OpenSourceSDRLab/PortaRF/hardware/portapack_h4m/h4-pcb/README.txt

This folder contains the PCB files for PortaPack H4. If you have any questions about the PCB files, please feel free to contact me. Thank you!

My email addresses are:
support@opensourcesdrlab.com
opensourcesdrlab@gmail.com
