OpenSourceSDRLab/PortaRF/docs/images/h2_cover.jpg

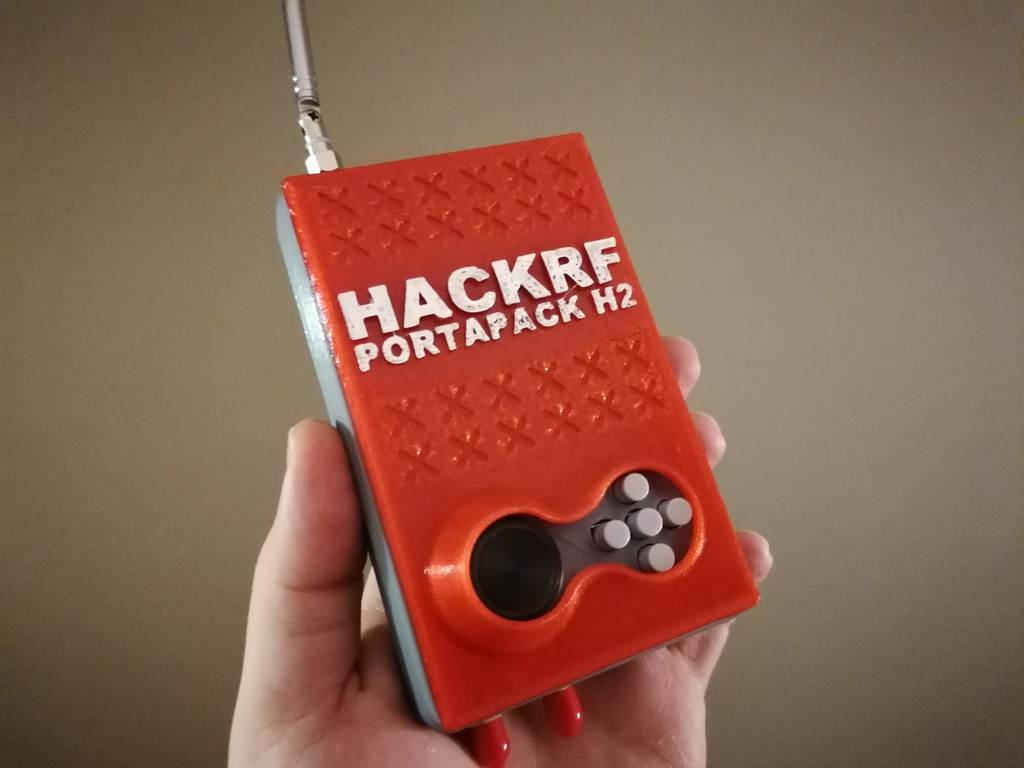
docs/images/h2_cover.jpg
