OpenSourceSDRLab/PortaRF/docs/images/h2_front.jpg

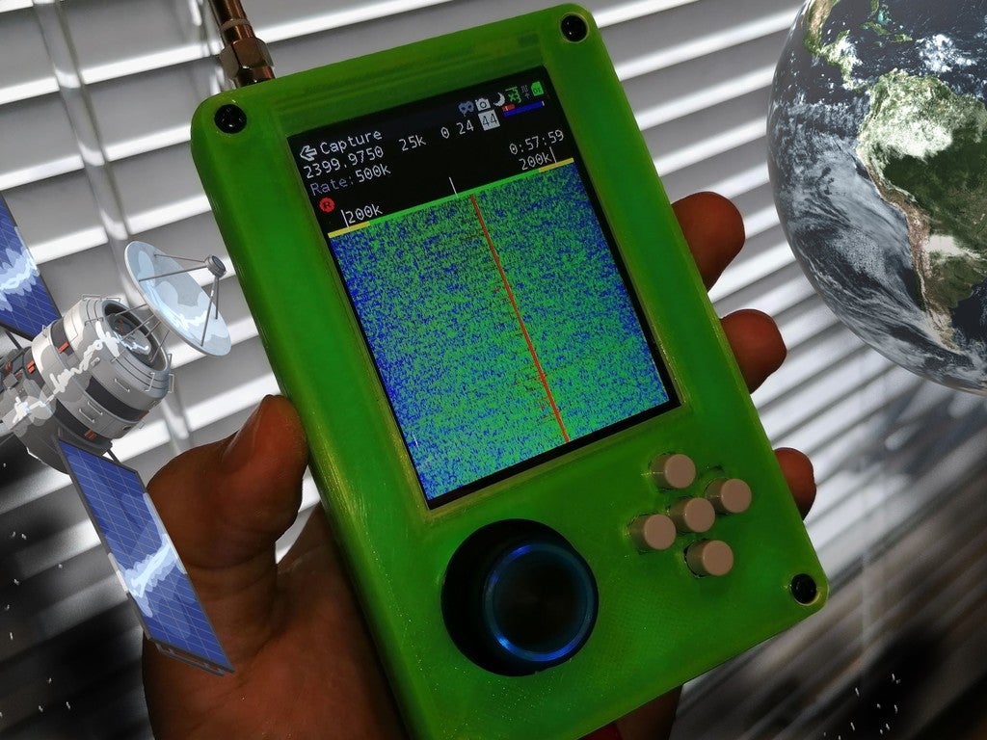
docs/images/h2_front.jpg
