OpenSourceSDRLab/PortaRF/firmware/chibios-portapack/ext/fatfs/doc/res/f7.png

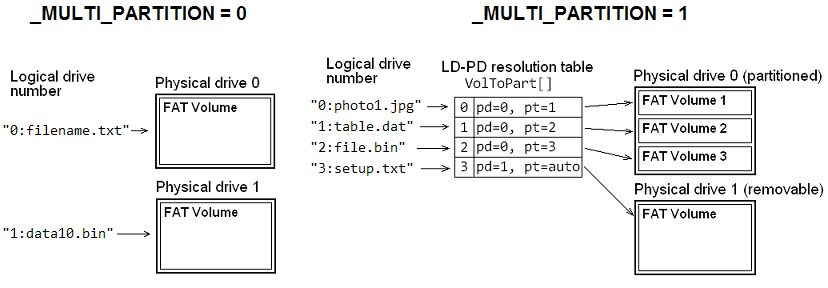
firmware/chibios-portapack/ext/fatfs/doc/res/f7.png
