OpenSourceSDRLab/PortaRF/firmware/chibios-portapack/ext/fatfs/doc/res/modules.png

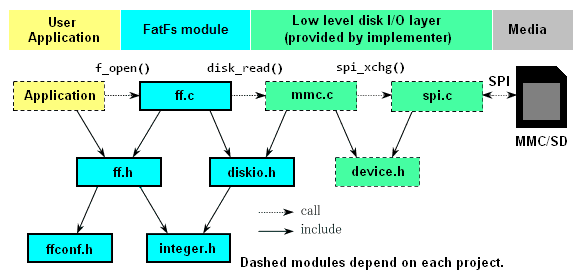
firmware/chibios-portapack/ext/fatfs/doc/res/modules.png
