OpenSourceSDRLab/PortaRF/hackrf/docs/images/block-diagram-r9.png

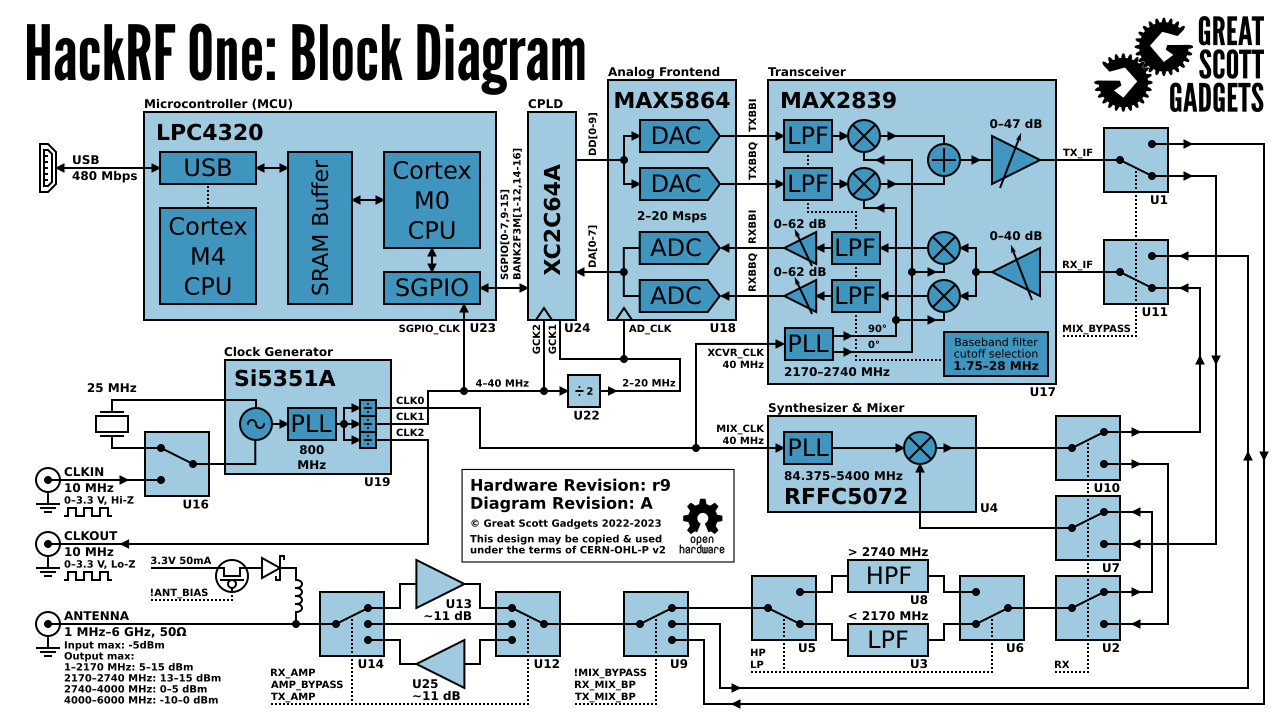
hackrf/docs/images/block-diagram-r9.png
