OpenSourceSDRLab/PortaRF/hackrf/docs/images/block-diagram.png

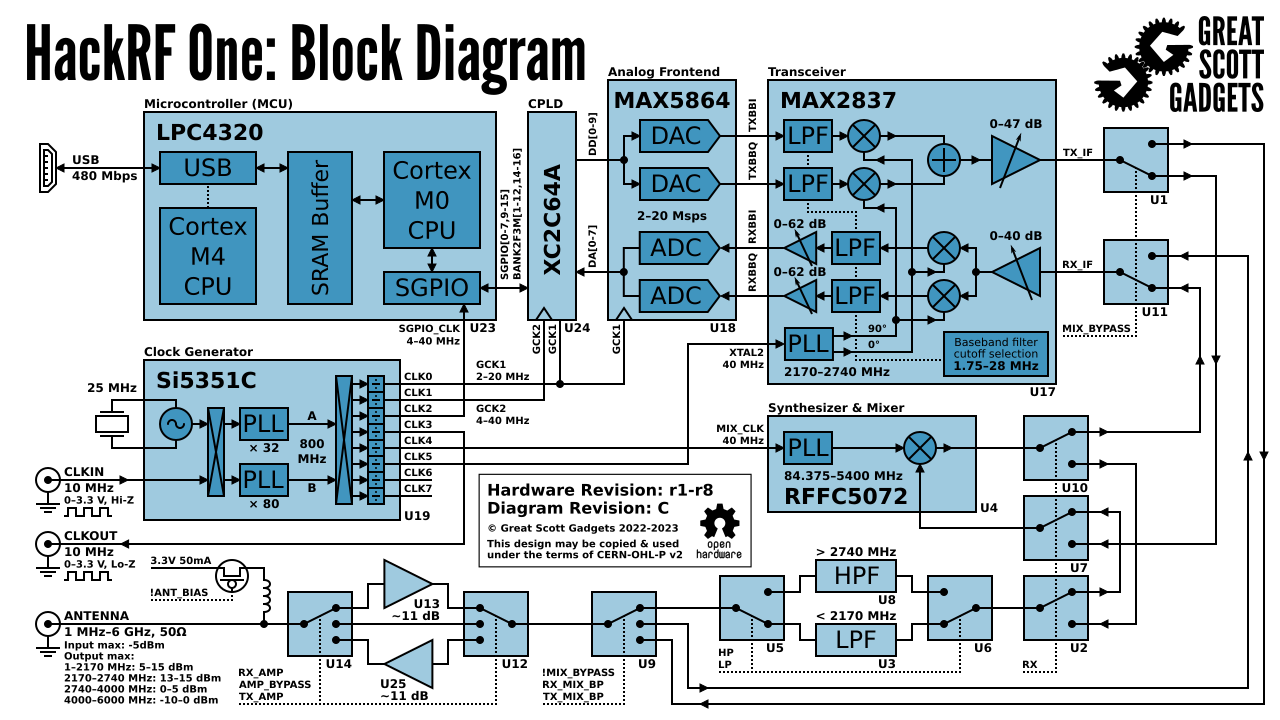
hackrf/docs/images/block-diagram.png
