OpenSourceSDRLab/PortaRF/hackrf/docs/images/grc-hw-sync-streaming.png

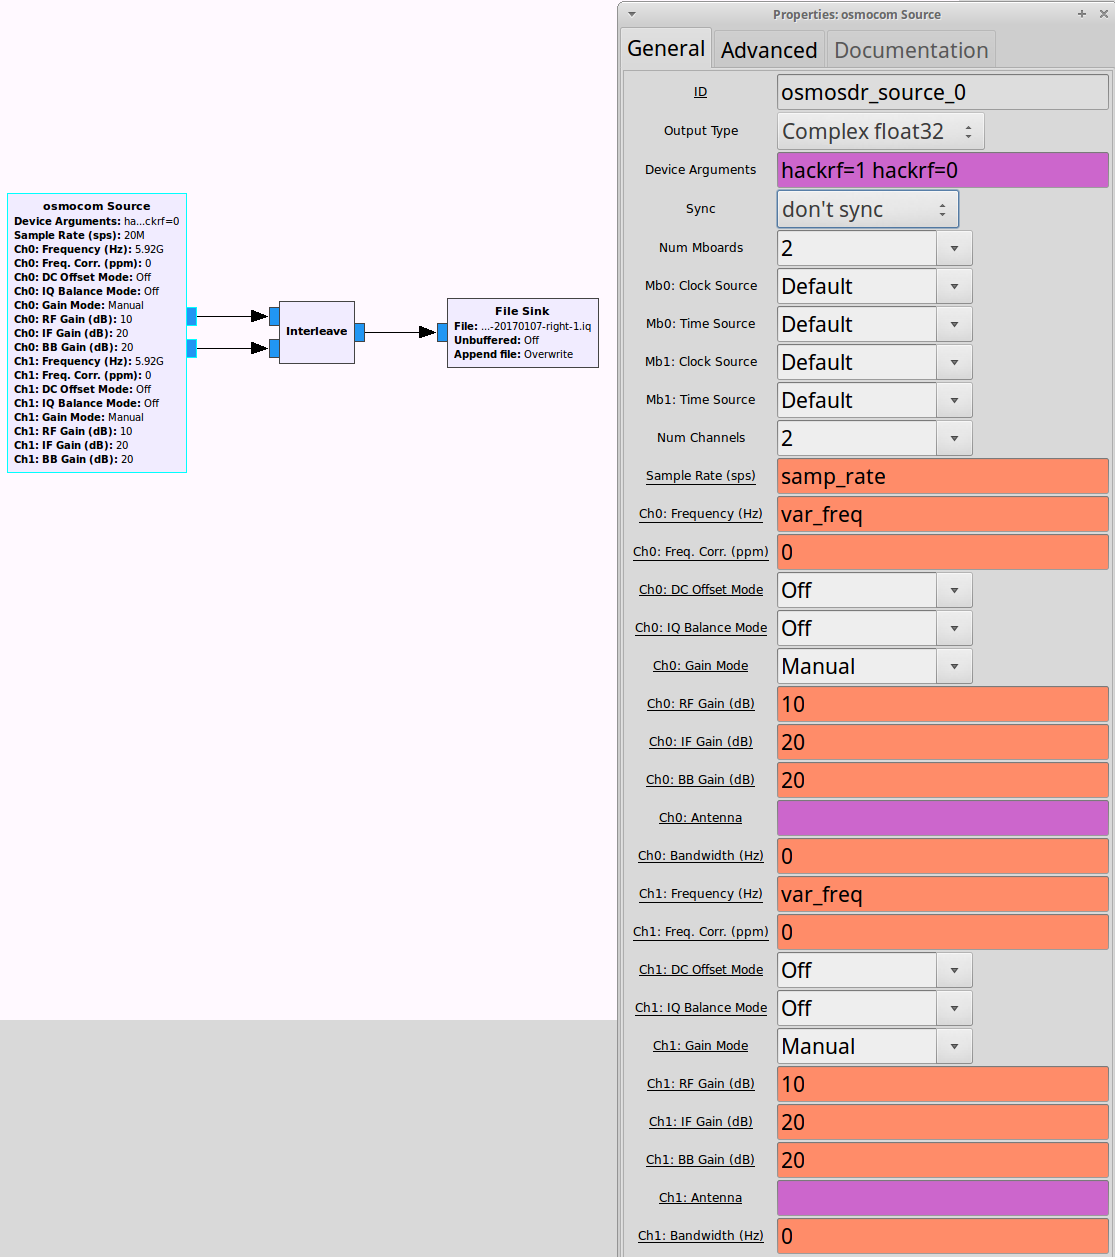
hackrf/docs/images/grc-hw-sync-streaming.png
