OpenSourceSDRLab/PortaRF/hackrf/docs/images/jawbreaker.JPG

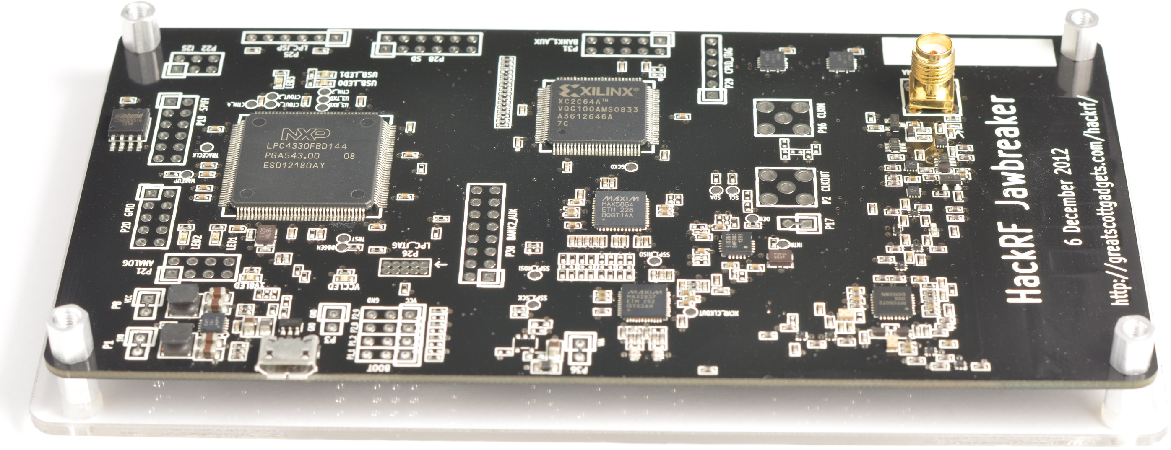
hackrf/docs/images/jawbreaker.JPG
