OpenSourceSDRLab/PortaRF/hackrf/docs/images/noisereducingcable.jpeg

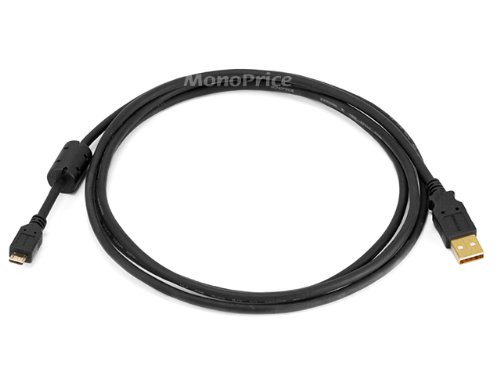
hackrf/docs/images/noisereducingcable.jpeg
