OpenSourceSDRLab/PortaRF/hackrf/docs/images/noisereducingcablescreenshot.jpeg

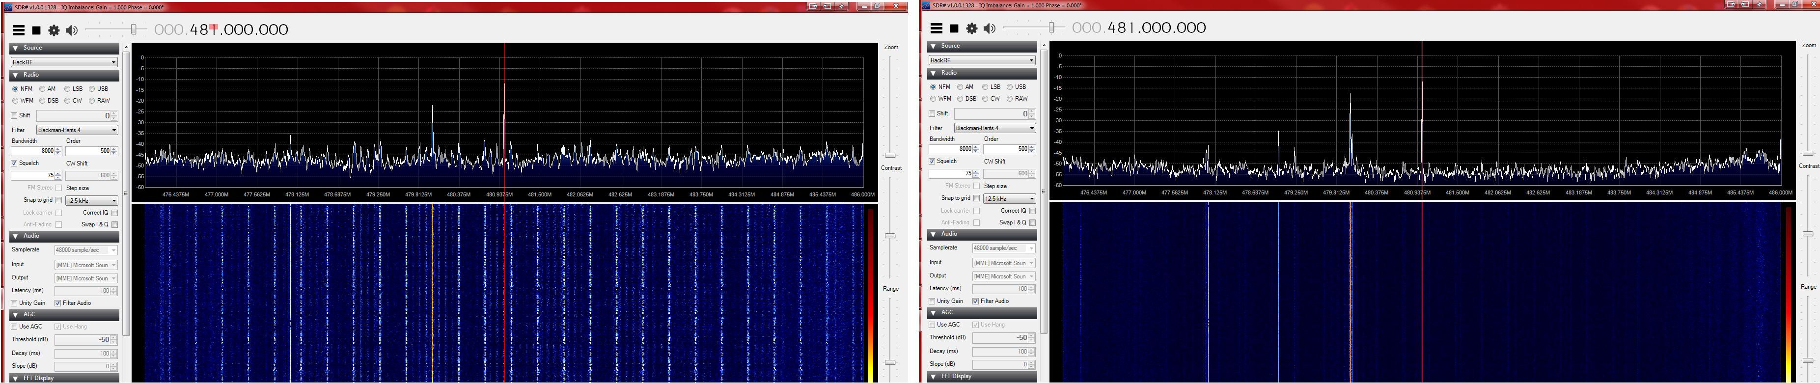
hackrf/docs/images/noisereducingcablescreenshot.jpeg
