OpenSourceSDRLab/PortaRF/hackrf/docs/images/operacake-block-diagram.png

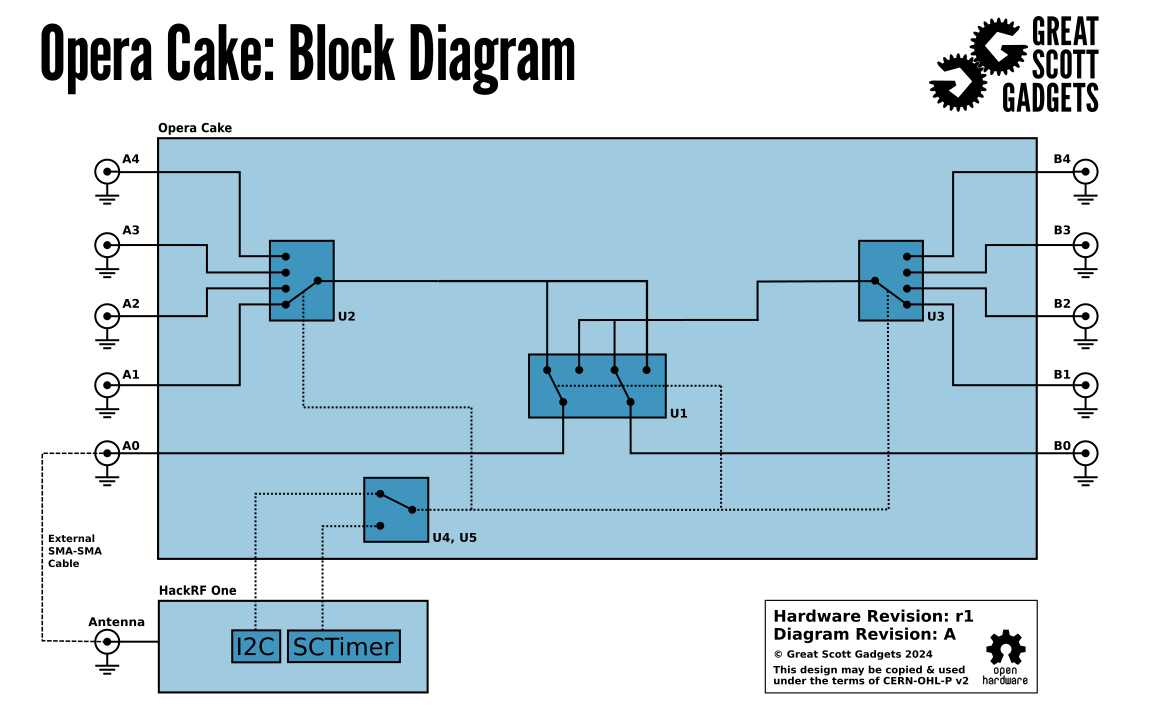
hackrf/docs/images/operacake-block-diagram.png
