OpenSourceSDRLab/PortaRF/hackrf/docs/images/operacake.jpeg

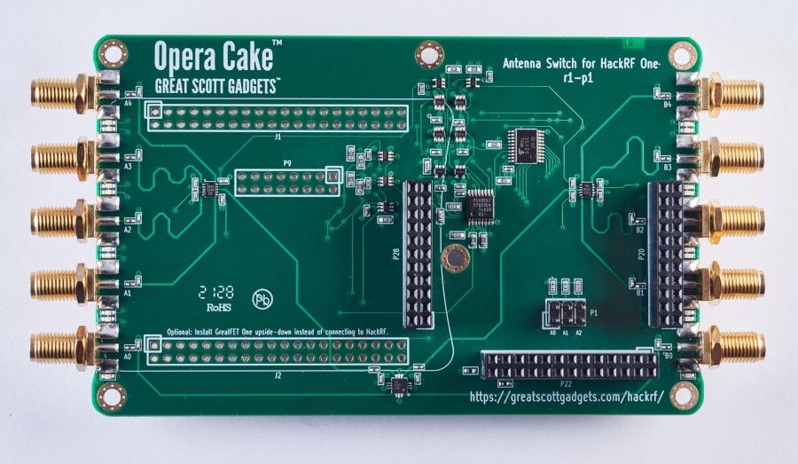
hackrf/docs/images/operacake.jpeg
