OpenSourceSDRLab/PortaRF/hackrf/docs/images/rf_shield_3.jpg

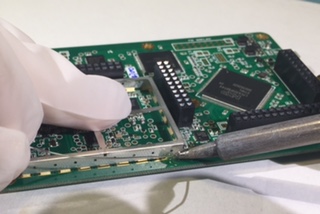
hackrf/docs/images/rf_shield_3.jpg
