OpenSourceSDRLab/PortaRF/hackrf/docs/images/rf_shield_4.jpg

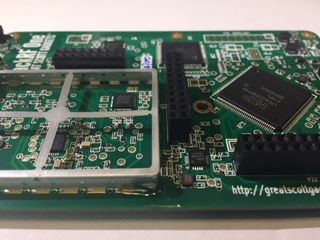
hackrf/docs/images/rf_shield_4.jpg
