OpenSourceSDRLab/PortaRF/hackrf/docs/images/rf_shield_5.jpg

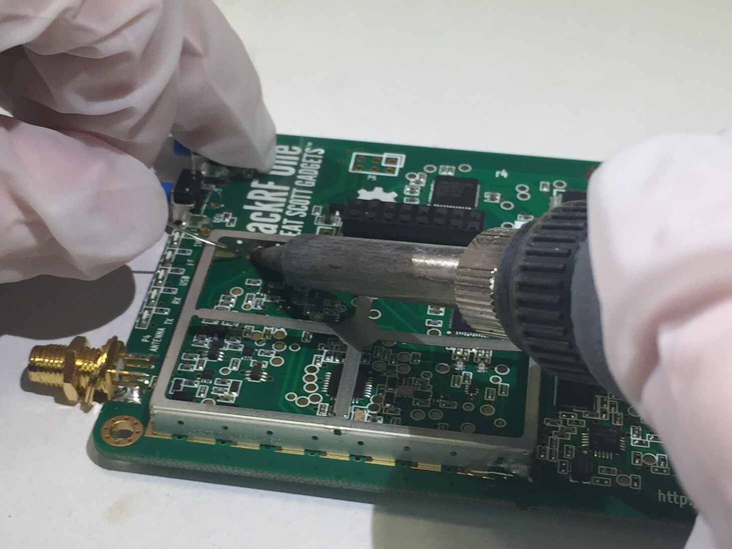
hackrf/docs/images/rf_shield_5.jpg
