OpenSourceSDRLab/PortaRF/hackrf/docs/images/rf_shield_6.jpg

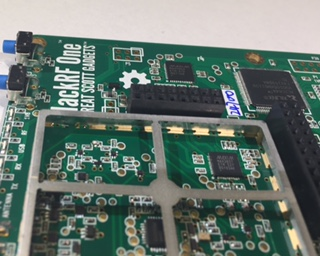
hackrf/docs/images/rf_shield_6.jpg
