OpenSourceSDRLab/PortaRF/hackrf/docs/images/trigger-pins.png

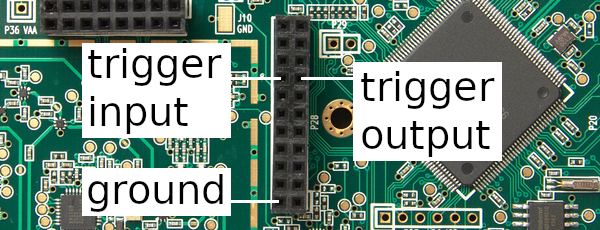
hackrf/docs/images/trigger-pins.png
