OpenSourceSDRLab/PortaRF/images/6afd1d4916e6c6b03d07bbbb10bda296.jpg

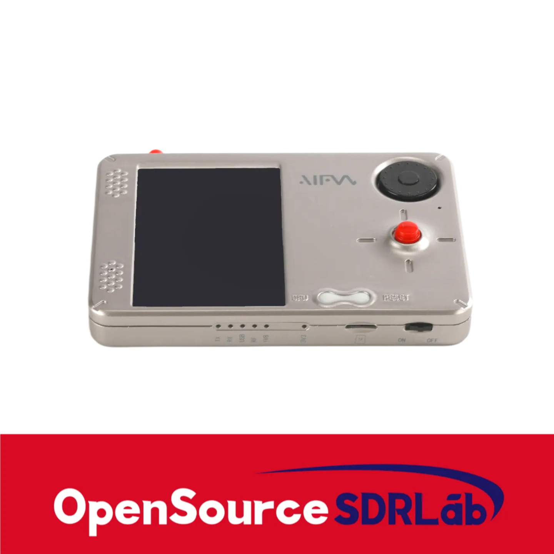
images/6afd1d4916e6c6b03d07bbbb10bda296.jpg
