OpenSourceSDRLab/PortaRF/images/069db5dcb38166e48cfb38b87b556339.jpg

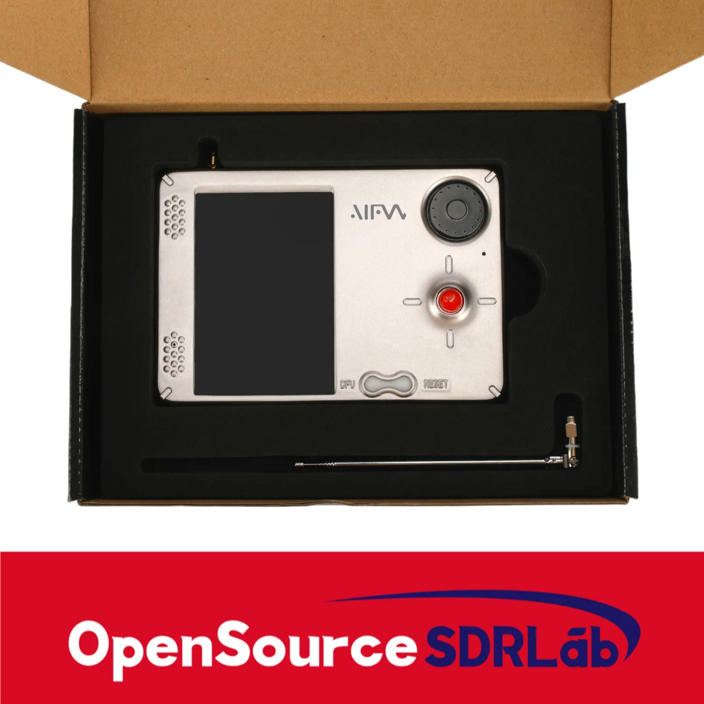
images/069db5dcb38166e48cfb38b87b556339.jpg
