OpenSourceSDRLab/PortaRF/images/0192db731e4ba467686fbc48f90995fa.jpg

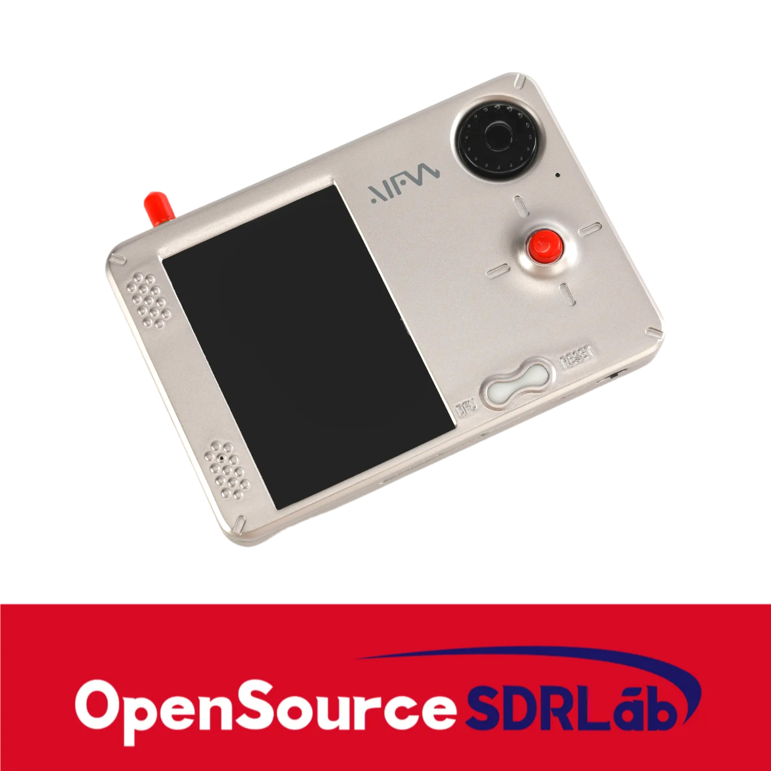
images/0192db731e4ba467686fbc48f90995fa.jpg
