OpenSourceSDRLab/PortaRF/images/1893cb14351a77d188c50b2f643207d6.jpg

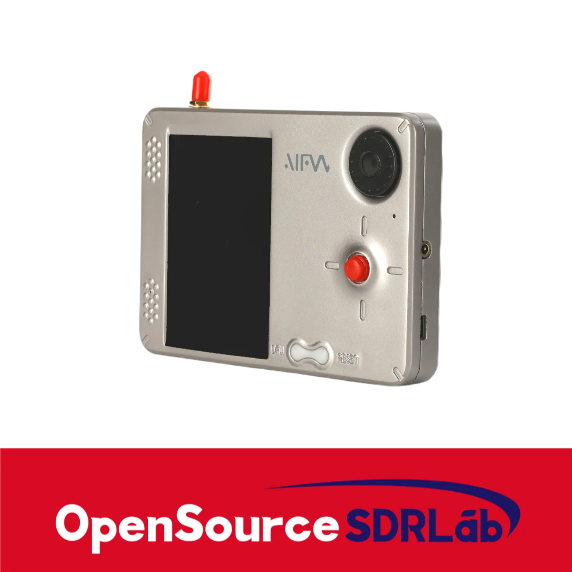
images/1893cb14351a77d188c50b2f643207d6.jpg
