OpenSourceSDRLab/PortaRF/images/09969ef1a2aa3e77349972c5e69b2ade.jpg

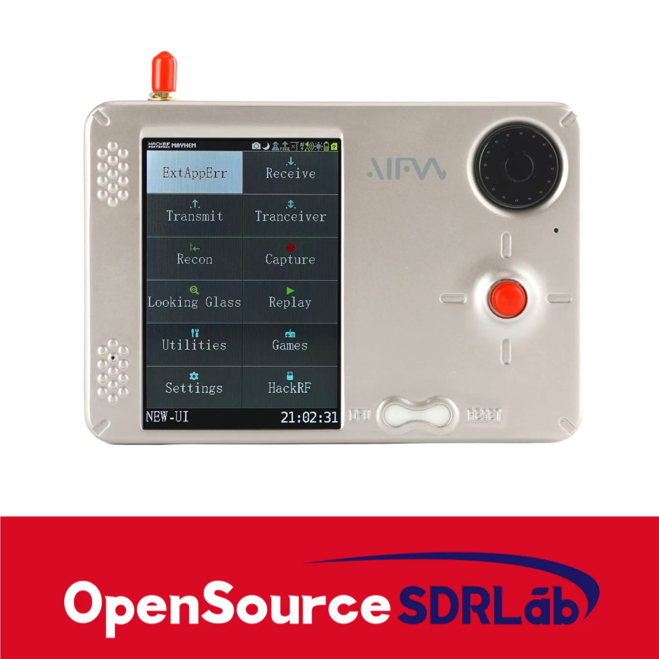
images/09969ef1a2aa3e77349972c5e69b2ade.jpg
