OpenSourceSDRLab/PortaRF/images/4067304609b4fa81f357f699b0781bd3.jpg

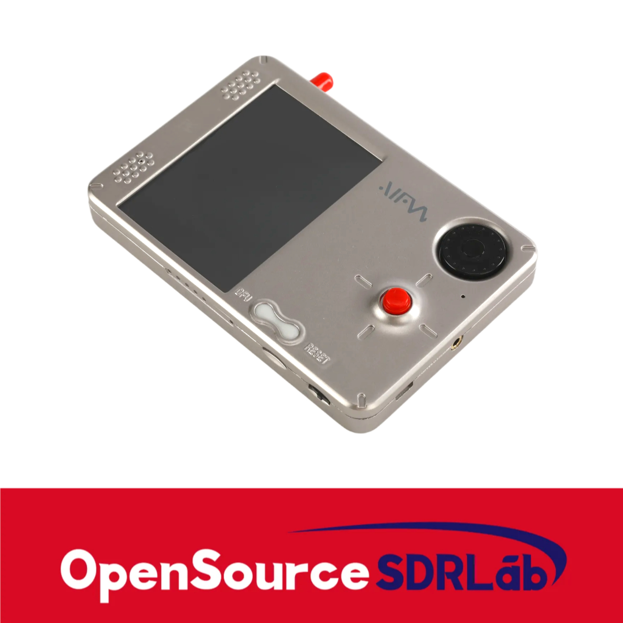
images/4067304609b4fa81f357f699b0781bd3.jpg
