OpenSourceSDRLab/PortaRF/images/device interface-1.jpg

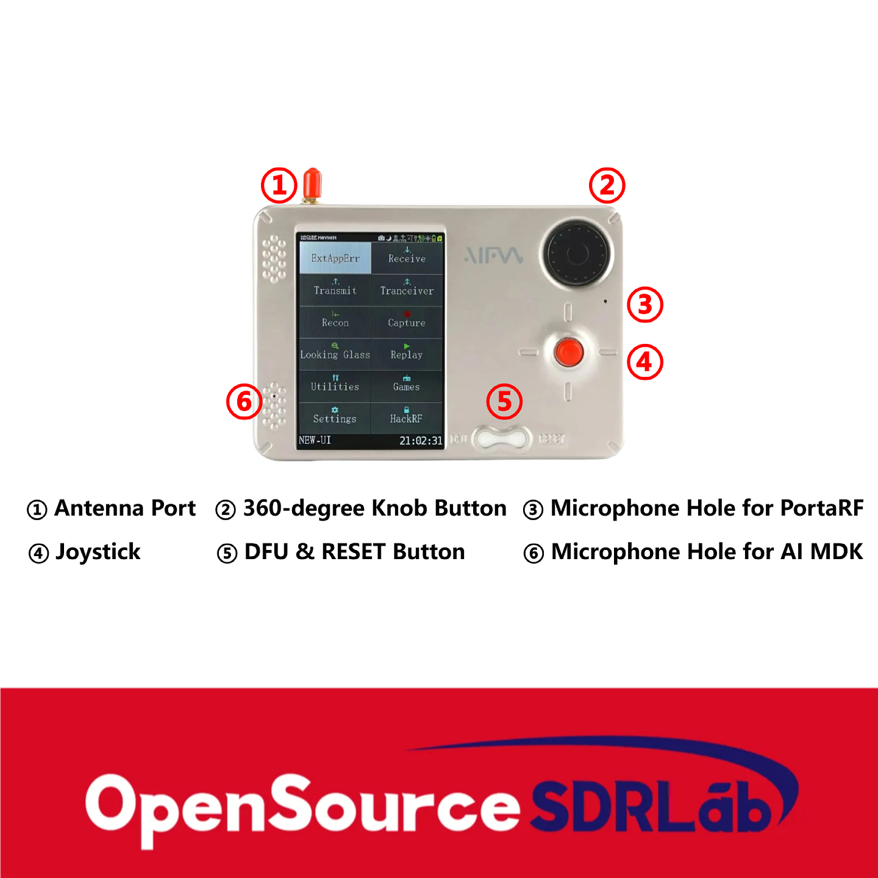
images/device interface-1.jpg
