OpenSourceSDRLab/PortaRF/images/device interface-2.jpg

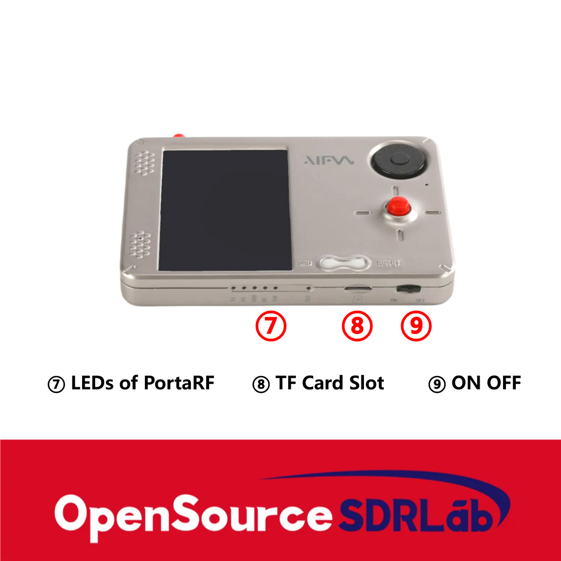
images/device interface-2.jpg
