OpenSourceSDRLab/PortaRF/images/device interface-3.jpg

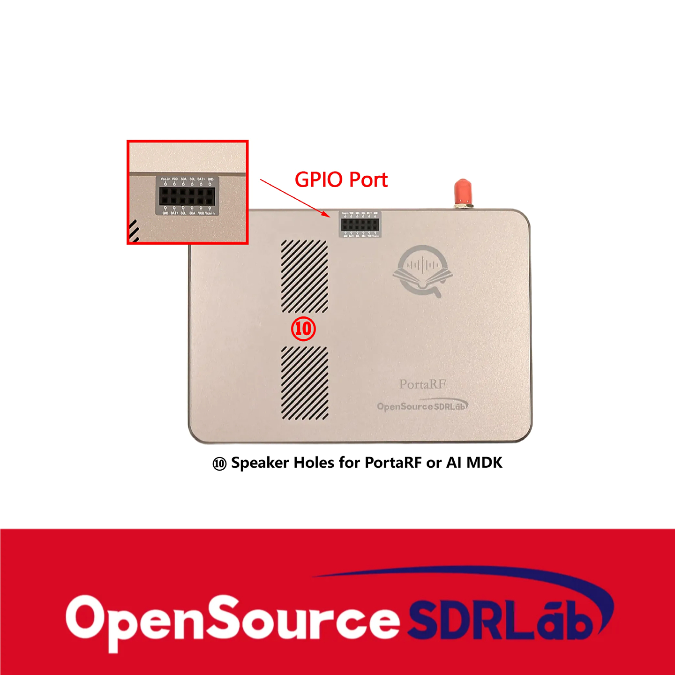
images/device interface-3.jpg
