OpenSourceSDRLab/PortaRF/sdcard/SAMPLES/LED/Aurora_RGB/remote.jpeg

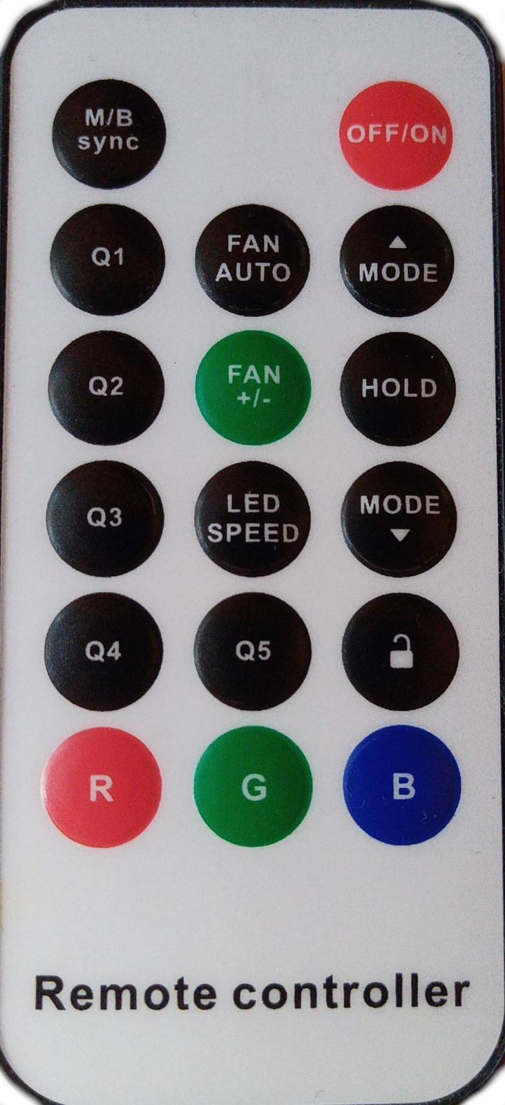
sdcard/SAMPLES/LED/Aurora_RGB/remote.jpeg
