OpenSourceSDRLab/PortaRF/sdcard/SSTV/320240BW.bmp

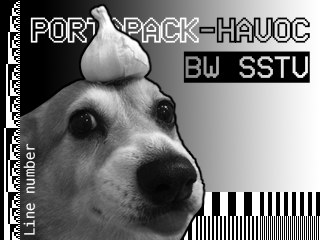
sdcard/SSTV/320240BW.bmp
