OpenSourceSDRLab/PortaRF/sdcard/SSTV/320256C.bmp

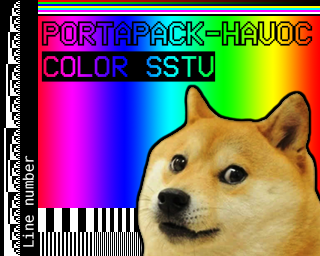
sdcard/SSTV/320256C.bmp
