OpenSourceSDRLab/PortaRF/sdcard/SSTV/sstvtest.bmp

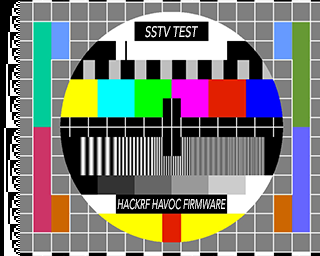
sdcard/SSTV/sstvtest.bmp
