OpenSourceSDRLab/PortaRF/firmware/application/apps/ble_tx_app.hpp

/*
 * Copyright (C) 2014 Jared Boone, ShareBrained Technology, Inc.
 * Copyright (C) 2017 Furrtek
 * Copyright (C) 2023 TJ Baginski
 *
 * This file is part of PortaPack.
 *
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
 * You should have received a copy of the GNU General Public License
 * along with this program; see the file COPYING.  If not, write to
 * the Free Software Foundation, Inc., 51 Franklin Street,
 * Boston, MA 02110-1301, USA.
 */

#ifndef __BLE_TX_APP_H__
#define __BLE_TX_APP_H__

#include "ui.hpp"
#include "ui_navigation.hpp"
#include "ui_receiver.hpp"
#include "ui_transmitter.hpp"
#include "ui_text_editor.hpp"
#include "ui_freq_field.hpp"
#include "ui_record_view.hpp"
#include "app_settings.hpp"
#include "radio_state.hpp"
#include "replay_thread.hpp"
#include "log_file.hpp"
#include "utility.hpp"
#include "file_path.hpp"

#include "ble_tx_app.hpp"

#include "recent_entries.hpp"

#include <string>
#include <memory>

class BLELoggerTx {
   public:
    Optional<File::Error> append(const std::filesystem::path& filename) {
        return log_file.append(filename);
    }

    void log_raw_data(const std::string& data);

   private:
    LogFile log_file{};
};

namespace ui {

enum PKT_TYPE {
    PKT_TYPE_INVALID_TYPE,
    PKT_TYPE_RAW,
    PKT_TYPE_DISCOVERY,
    PKT_TYPE_IBEACON,
    PKT_TYPE_ADV_IND,
    PKT_TYPE_ADV_DIRECT_IND,
    PKT_TYPE_ADV_NONCONN_IND,
    PKT_TYPE_ADV_SCAN_IND,
    PKT_TYPE_SCAN_REQ,
    PKT_TYPE_SCAN_RSP,
    PKT_TYPE_CONNECT_REQ,
    PKT_TYPE_LL_DATA,
    PKT_TYPE_LL_CONNECTION_UPDATE_REQ,
    PKT_TYPE_LL_CHANNEL_MAP_REQ,
    PKT_TYPE_LL_TERMINATE_IND,
    PKT_TYPE_LL_ENC_REQ,
    PKT_TYPE_LL_ENC_RSP,
    PKT_TYPE_LL_START_ENC_REQ,
    PKT_TYPE_LL_START_ENC_RSP,
    PKT_TYPE_LL_UNKNOWN_RSP,
    PKT_TYPE_LL_FEATURE_REQ,
    PKT_TYPE_LL_FEATURE_RSP,
    PKT_TYPE_LL_PAUSE_ENC_REQ,
    PKT_TYPE_LL_PAUSE_ENC_RSP,
    PKT_TYPE_LL_VERSION_IND,
    PKT_TYPE_LL_REJECT_IND,
    PKT_TYPE_NUM_PKT_TYPE
};

struct BLETxPacket {
    char macAddress[13];
    char advertisementData[63];
    char packetCount[11];
    char packetType[17];
    uint32_t packet_count;
    PKT_TYPE pduType;
};

class BLETxView : public View {
   public:
    BLETxView(NavigationView& nav);
    BLETxView(NavigationView& nav, BLETxPacket packet);
    ~BLETxView();

    void set_parent_rect(const Rect new_parent_rect) override;
    void paint(Painter&) override {};

    void focus() override;

    bool is_active() const;
    void toggle();
    void start();
    void send_packet();
    void stop();
    void handle_replay_thread_done(const uint32_t return_code);
    void file_error();
    bool saveFile(const std::filesystem::path& path);

    std::string title() const override { return "BLE TX"; };

   private:
    void on_timer();
    void on_data(uint32_t value, bool is_data);
    void on_file_changed(const std::filesystem::path& new_file_path);
    void on_save_file(const std::string value);
    void on_tx_progress(const bool done, uint32_t progress);
    void on_random_data_change(std::string value);
    void update_current_packet(BLETxPacket packet, uint32_t currentIndex);
    static OptionsField::options_t build_channel_options();

    NavigationView& nav_;
    TxRadioState radio_state_{
        2'402'000'000 /* frequency */,
        4'000'000 /* bandwidth */,
        4'000'000 /* sampling rate */
    };
    app_settings::SettingsManager settings_{
        "tx_ble", app_settings::Mode::TX};

    uint8_t console_color{0};
    uint32_t prev_value{0};

    std::filesystem::path file_path{};
    std::filesystem::path packet_save_path{bletx_dir / u"BLETX_????.TXT"};
    uint8_t channel_number = 37;
    bool auto_channel = false;

    char randomMac[13] = "010203040506";

    bool is_running = false;

    int16_t timer_count{0};
    int16_t timer_period{1};
    uint8_t auto_channel_start_number = 37;
    uint8_t auto_channel_send_count = 0;

    bool repeatLoop = false;
    uint32_t packet_counter{0};
    uint32_t num_packets{0};
    uint32_t current_packet{0};
    uint8_t packetTxCount{0};
    bool packetDone = false;
    bool random_mac = false;
    bool file_override = false;

    typedef struct {
        uint16_t line;
        uint16_t col;
    } CursorPos;

    std::unique_ptr<FileWrapper> dataFileWrapper{};
    File dataFile{};
    std::filesystem::path dataTempFilePath{bletx_dir / u"dataFileTemp.TXT"};
    std::vector<uint16_t> markedBytes{};
    CursorPos cursor_pos{};
    uint8_t marked_counter = 0;

    static constexpr uint8_t mac_address_size_str{12};
    static constexpr uint8_t max_packet_size_str{62};
    static constexpr uint8_t max_packet_repeat_str{10};
    static constexpr uint8_t max_packet_type_str{16};
    static constexpr uint32_t max_packet_repeat_count{UINT32_MAX};
    static constexpr uint32_t max_num_packets{32};

    BLETxPacket packets[max_num_packets];

    static constexpr auto header_height = 10 * 16;
    static constexpr auto switch_button_height = 6 * 16;

    Button button_open{
        {UI_POS_X(0), UI_POS_Y(0), 10 * 8, 2 * 16},
        "Open file"};

    Text text_filename{
        {11 * 8, UI_POS_Y(0), UI_POS_WIDTH_REMAINING(11), 16},
        "-"};

    ProgressBar progressbar{
        {11 * 8, 1 * 16, UI_POS_WIDTH_REMAINING(11 + 10), 16}};

    Checkbox check_rand_mac{
        {UI_POS_X_RIGHT(9), 1 * 16},
        6,
        "?? Mac",
        true};

    TxFrequencyField field_frequency{
        {UI_POS_X(0), 2 * 16},
        nav_};

    TransmitterView2 tx_view{
        {11 * 8, 2 * 16},
        /*short_ui*/ true};

    Checkbox check_loop{
        {UI_POS_X_RIGHT(9), 2 * 16},
        4,
        "Loop",
        true};

    ImageButton button_play{
        {UI_POS_X_RIGHT(2), 2 * 16, 2 * 8, 1 * 16},
        &bitmap_play,
        Theme::getInstance()->fg_green->foreground,
        Theme::getInstance()->fg_green->background};

    Labels label_speed{
        {{UI_POS_X(0), 6 * 8}, "Speed:", Theme::getInstance()->fg_light->foreground}};

    OptionsField options_speed{
        {7 * 8, 6 * 8},
        3,
        {{"1 ", 2},     // 25ms
         {"2 ", 4},     // 50ms
         {"3 ", 6},     // 75ms
         {"4 ", 8},     // 100ms
         {"5 ", 12}}};  // 150ms

    OptionsField options_channel{
        {11 * 8, 6 * 8},
        5,
        {}};

    OptionsField options_adv_type{
        {17 * 8, 6 * 8},
        14,
        {{"DISCOVERY ", PKT_TYPE_DISCOVERY},
         {"ADV_IND", PKT_TYPE_ADV_IND},
         {"ADV_DIRECT", PKT_TYPE_ADV_DIRECT_IND},
         {"ADV_NONCONN", PKT_TYPE_ADV_NONCONN_IND},
         {"ADV_SCAN_IND", PKT_TYPE_ADV_SCAN_IND},
         {"SCAN_REQ", PKT_TYPE_SCAN_REQ},
         {"SCAN_RSP", PKT_TYPE_SCAN_RSP},
         {"CONNECT_REQ", PKT_TYPE_CONNECT_REQ}}};

    Labels label_marked_data{
        {{UI_POS_X(0), 4 * 16}, "Marked Data:", Theme::getInstance()->fg_light->foreground}};

    OptionsField marked_data_sequence{
        {12 * 8, 8 * 8},
        8,
        {{"Ascend", 0},
         {"Descend", 1},
         {"Random", 2}}};

    Labels label_packet_index{
        {{UI_POS_X(0), 12 * 8}, "Packet Index:", Theme::getInstance()->fg_light->foreground}};

    Text text_packet_index{
        {13 * 8, 6 * 16, 12 * 8, 16},
        "-"};

    Labels label_packets_sent{
        {{UI_POS_X(0), 14 * 8}, "Repeat Count:", Theme::getInstance()->fg_light->foreground}};

    Text text_packets_sent{
        {13 * 8, 7 * 16, 12 * 8, 16},
        "-"};

    Labels label_mac_address{
        {{UI_POS_X(0), 16 * 8}, "Mac Address:", Theme::getInstance()->fg_light->foreground}};

    Text text_mac_address{
        {12 * 8, 8 * 16, 20 * 8, 16},
        "-"};

    Labels label_data_packet{
        {{UI_POS_X(0), 9 * 16}, "Packet Data:", Theme::getInstance()->fg_light->foreground}};

    TextViewer dataEditView{
        {0, 9 * 18, 240, 240}};

    Button button_clear_marked{
        {UI_POS_X(1), UI_POS_Y_BOTTOM(5), UI_POS_WIDTH(13), UI_POS_HEIGHT(1.5)},
        "Clear Marked"};

    Button button_save_packet{
        {UI_POS_X(1), UI_POS_Y_BOTTOM(3), UI_POS_WIDTH(13), UI_POS_HEIGHT(2)},
        "Save Packet"};

    Button button_switch{
        {UI_POS_X_RIGHT(14), UI_POS_Y_BOTTOM(3), UI_POS_WIDTH(13), UI_POS_HEIGHT(2)},
        "Switch to Rx"};

    std::string str_log{""};
    bool logging{true};
    bool logging_done{false};
    std::string packetFileBuffer{};

    std::unique_ptr<BLELoggerTx> logger{};

    MessageHandlerRegistration message_handler_packet{
        Message::ID::AFSKData,
        [this](Message* const p) {
            const auto message = static_cast<const AFSKDataMessage*>(p);
            this->on_data(message->value, message->is_data);
        }};

    MessageHandlerRegistration message_handler_tx_progress{
        Message::ID::TXProgress,
        [this](const Message* const p) {
            const auto message = *reinterpret_cast<const TXProgressMessage*>(p);
            this->on_tx_progress(message.done, message.progress);
        }};

    MessageHandlerRegistration message_handler_frame_sync{
        Message::ID::DisplayFrameSync,
        [this](const Message* const) {
            this->on_timer();
        }};
};

} /* namespace ui */

#endif /*__UI_AFSK_RX_H__*/
