OpenSourceSDRLab/PortaRF/firmware/application/apps/ui_debug.hpp

/*
 * Copyright (C) 2015 Jared Boone, ShareBrained Technology, Inc.
 * Copyright (C) 2024 Mark Thompson
 * Copyright (C) 2024 u-foka
 *
 * This file is part of PortaPack.
 *
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
 * You should have received a copy of the GNU General Public License
 * along with this program; see the file COPYING.  If not, write to
 * the Free Software Foundation, Inc., 51 Franklin Street,
 * Boston, MA 02110-1301, USA.
 */

#ifndef __UI_DEBUG_H__
#define __UI_DEBUG_H__

#include "ui.hpp"
#include "ui_widget.hpp"
#include "ui_painter.hpp"
#include "ui_menu.hpp"
#include "ui_navigation.hpp"

#include "rffc507x.hpp"
#include "portapack.hpp"
#include "memory_map.hpp"
#include "irq_controls.hpp"

#include <functional>
#include <utility>

namespace ui {

class DebugMemoryView : public View {
   public:
    DebugMemoryView(NavigationView& nav);

    void focus() override;

    std::string title() const override { return "Memory"; };

   private:
    Text text_title{
        {72, 96, 96, 16},
        "Memory Usage",
    };

    Text text_label_m0_core_free{
        {0, 128, 144, 16},
        "M0 Core Free Bytes",
    };

    Text text_label_m0_core_free_value{
        {200, 128, 40, 16},
    };

    Text text_label_m0_heap_fragmented_free{
        {0, 144, 184, 16},
        "M0 Heap Fragmented Free",
    };

    Text text_label_m0_heap_fragmented_free_value{
        {200, 144, 40, 16},
    };

    Text text_label_m0_heap_fragments{
        {0, 160, 136, 16},
        "M0 Heap Fragments",
    };

    Text text_label_m0_heap_fragments_value{
        {200, 160, 40, 16},
    };

    Button button_done{
        {72, 192, 96, 24},
        "Done"};
};

typedef enum {
    CT_PMEM,
    CT_RFFC5072,
    CT_MAX283X,
    CT_SI5351,
    CT_AUDIO,
    CT_MAX17055,
} chip_type_t;

struct RegistersWidgetConfig {
    chip_type_t chip_type;
    uint32_t registers_count;
    uint32_t registers_per_page;
    uint32_t register_bits;

    constexpr size_t legend_length() const {
        return (registers_count >= 0x10) ? 2 : 1;
    }

    constexpr size_t legend_width() const {
        return legend_length() * 8;
    }

    constexpr size_t value_length() const {
        return (register_bits + 3) / 4;
    }

    constexpr size_t value_width() const {
        return value_length() * 8;
    }

    constexpr size_t registers_per_row() const {
        return (value_length() >= 3) ? 4 : 8;
    }

    constexpr size_t registers_row_length() const {
        return (registers_per_row() * (value_length() + 1)) - 1;
    }

    constexpr size_t registers_row_width() const {
        return registers_row_length() * 8;
    }

    constexpr size_t row_width() const {
        return legend_width() + 8 + registers_row_width();
    }

    constexpr size_t rows() const {
        return registers_count / registers_per_row();
    }
};

class RegistersWidget : public Widget {
   public:
    RegistersWidget(RegistersWidgetConfig&& config);

    void update();

    void paint(Painter& painter) override;

    uint32_t reg_read(const uint32_t register_number);
    void reg_write(const uint32_t register_number, const uint32_t value);

    void set_page(int32_t value) { page_number = value; }
    uint32_t page(void) { return page_number; }
    uint32_t page_count(void) { return (config.registers_count + config.registers_per_page - 1) / config.registers_per_page; }

   private:
    const RegistersWidgetConfig config;
    uint32_t page_number;

    static constexpr size_t row_height = 16;

    void draw_legend(const Coord left, Painter& painter);
    void draw_values(const Coord left, Painter& painter);
};

class RegistersView : public View {
   public:
    RegistersView(NavigationView& nav, const std::string& title, RegistersWidgetConfig&& config);
    void focus() override;
    bool on_encoder(const EncoderEvent delta) override;

   private:
    Text text_title{};

    RegistersWidget registers_widget;

    Button button_update{
        {16, 280, 96, 24},
        "Update"};

    Button button_done{
        {128, 280, 96, 24},
        "Done"};

    Button button_write{
        {144, 248, 80, 20},
        "Write"};

    Labels labels{
        {{1 * 8, 248}, "Reg:", Theme::getInstance()->fg_light->foreground},
        {{8 * 8, 248}, "Data:", Theme::getInstance()->fg_light->foreground}};

    SymField field_write_reg_num{
        {5 * 8, 248},
        2,
        SymField::Type::Hex};

    SymField field_write_data_val{
        {13 * 8, 248},
        4,
        SymField::Type::Hex};
};

class ControlsSwitchesWidget : public Widget {
   public:
    ControlsSwitchesWidget(
        Rect parent_rect)
        : Widget{parent_rect},
          key_event_mask(0),
          long_press_key_event_mask{0},
          last_delta{0} {
        set_focusable(true);
    }

    void on_show() override;
    bool on_key(const KeyEvent key) override;
    bool on_encoder(const EncoderEvent delta) override;

    void paint(Painter& painter) override;

   private:
    uint8_t key_event_mask;
    uint8_t long_press_key_event_mask;
    EncoderEvent last_delta;

    MessageHandlerRegistration message_handler_frame_sync{
        Message::ID::DisplayFrameSync,
        [this](const Message* const) {
            this->on_frame_sync();
        }};

    void on_frame_sync();
};

class DebugControlsView : public View {
   public:
    explicit DebugControlsView(NavigationView& nav);

    void focus() override;

    std::string title() const override { return "Buttons Test"; };

   private:
    Labels labels{
        {{UI_POS_X_CENTER(14), 1 * 16}, "Controls State", Theme::getInstance()->bg_darkest->foreground},
        {{UI_POS_X(0), 11 * 16}, "Dial:", Theme::getInstance()->fg_medium->foreground},
        {{UI_POS_X(0), 14 * 16}, "Long-Press Mode:", Theme::getInstance()->fg_medium->foreground}};

    ControlsSwitchesWidget switches_widget{
        {80, 80, 80, 112},
    };

    OptionsField options_switches_mode{
        {17 * 8, 14 * 16},
        8,
        {
            {"Disabled", 0},
            {"Enabled", 0xFF},  // all KeyEvent bits to long-press mode
        }};

    Button button_done{
        {UI_POS_X_CENTER(12), 264, 96, 24},
        "Done"};
};

class DebugMemoryDumpView : public View {
   public:
    DebugMemoryDumpView(NavigationView& nav);
    void focus() override;
    std::string title() const override { return "Memory Dump"; };

   private:
    Button button_dump{
        {UI_POS_X_CENTER(12), 4 * 16, 96, 24},
        "Dump"};

    Button button_read{
        {UI_POS_X_CENTER(12) - UI_POS_WIDTH(10), 11 * 16, 96, 24},
        "Read"};

    Button button_write{
        {UI_POS_X_CENTER(12) + UI_POS_WIDTH(10), 11 * 16, 96, 24},
        "Write"};

    Button button_done{
        {UI_POS_X_RIGHT(12), UI_POS_Y_BOTTOM(3), 96, 24},
        "Done"};

    Labels labels{
        {{5 * 8, 1 * 16}, "Dump Range to File", Theme::getInstance()->fg_yellow->foreground},
        {{UI_POS_X(0), 2 * 16}, "Starting Address: 0x", Theme::getInstance()->fg_light->foreground},
        {{UI_POS_X(0), 3 * 16}, "Byte Count:       0x", Theme::getInstance()->fg_light->foreground},
        {{3 * 8, 8 * 16}, "Read/Write Single Word", Theme::getInstance()->fg_yellow->foreground},
        {{UI_POS_X(0), 9 * 16}, "Memory Address:   0x", Theme::getInstance()->fg_light->foreground},
        {{UI_POS_X(0), 10 * 16}, "Data Value:       0x", Theme::getInstance()->fg_light->foreground}};

    SymField field_starting_address{
        {20 * 8, 2 * 16},
        8,
        SymField::Type::Hex};

    SymField field_byte_count{
        {20 * 8, 3 * 16},
        8,
        SymField::Type::Hex};

    SymField field_rw_address{
        {20 * 8, 9 * 16},
        8,
        SymField::Type::Hex};

    SymField field_data_value{
        {20 * 8, 10 * 16},
        8,
        SymField::Type::Hex};
};

class DebugPmemView : public View {
   public:
    DebugPmemView(NavigationView& nav);
    void focus() override;
    bool on_encoder(const EncoderEvent delta) override;
    std::string title() const override { return "P.Mem Debug"; }

   private:
    static constexpr uint8_t page_size{96};  // Must be multiply of 4 otherwise bit shifting for register view wont work properly
    static constexpr uint8_t page_count{(portapack::memory::map::backup_ram.size() + page_size - 1) / page_size};

    RegistersWidget registers_widget;

    Text text_checksum{{16, 232, 208, 16}};
    Text text_checksum2{{16, 248, 208, 16}};

    Button button_ok{
        {screen_width / 3, 270, screen_width / 3, 24},
        "OK",
    };

    void update();
};

class DebugScreenTest : public View {
   public:
    DebugScreenTest(NavigationView& nav);
    bool on_key(KeyEvent key) override;
    bool on_encoder(EncoderEvent delta) override;
    bool on_touch(TouchEvent event) override;
    void paint(Painter& painter) override;

   private:
    NavigationView& nav_;
    Point pen_pos{};
    Color pen_color{0};
    int16_t pen_size{10};
};

/*class DebugLCRView : public View {
public:
        DebugLCRView(NavigationView& nav, std::string lcrstring);

        void focus() override;

        std::string title() const override { return "LCR debug"; };

private:
        Console console {
                { 8, 16, 224, screen_height-80 }
        };

        Button button_exit {
                { 72, 264, 96, 32 },
                "Exit"
        };
};*/

class DebugPeripheralsMenuView : public BtnGridView {
   public:
    DebugPeripheralsMenuView(NavigationView& nav);
    std::string title() const override { return "Peripherals"; };

   private:
    NavigationView& nav_;
    void on_populate() override;
};

class DebugReboot : public BtnGridView {
   public:
    DebugReboot(NavigationView& nav);

   private:
    void on_populate() override;
};

class DebugMenuView : public BtnGridView {
   public:
    DebugMenuView(NavigationView& nav);
    std::string title() const override { return "Debug"; };

   private:
    NavigationView& nav_;
    void on_populate() override;
};



class AudioDiagView : public View 
{
public:
    AudioDiagView(NavigationView& nav);
    void focus() override;
    std::string title() const override { return "audio I2C"; };

private:
    void print_line(const std::string& s);

    // 三个测试动作
    void test_probe();
    void test_write_once();
    void test_stress();

    Console console{{0, 0, 240, 240}};                // 高度缩小，留出按钮区
    Button button_probe{{0, 244, 80, 24}, "Probe"};
    Button button_write{{80, 244, 80, 24}, "Write"};
    Button button_stress{{160, 244, 80, 24}, "Stress"};
    Button button_done{{80, 272, 80, 24}, "Done"};
};


} /* namespace ui */

#endif /*__UI_DEBUG_H__*/
